joaoneves792/AviationRadio/3dmodels/potSupport.FCStd

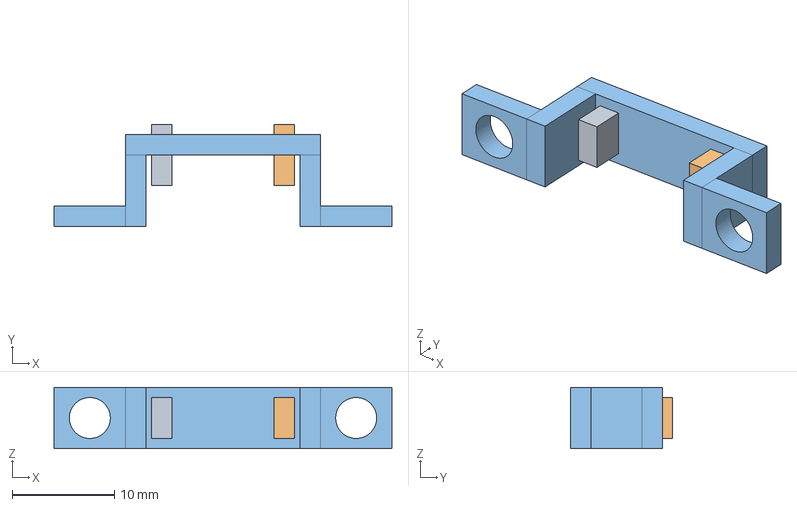
[picture p17: CAD file, 2021-02-12]
3dmodels/potSupport.FCStd
33.0 x 10.0 x 6.00 mm
