joaoneves792/AviationRadio/3dmodels/MXterst.FCStd

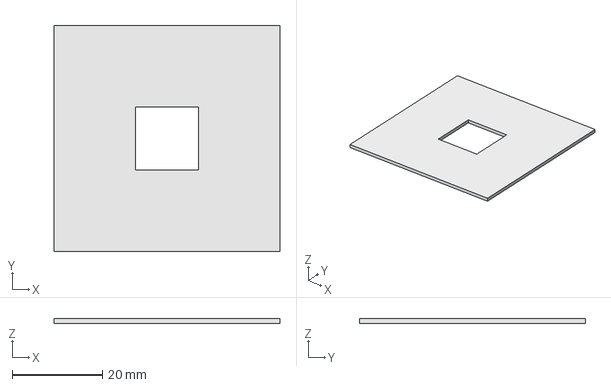
[picture p18: CAD file, 2021-02-12]
3dmodels/MXterst.FCStd
50.0 x 50.0 x 1.00 mm
