joaoneves792/AviationRadio/3dmodels/MXtest.stl

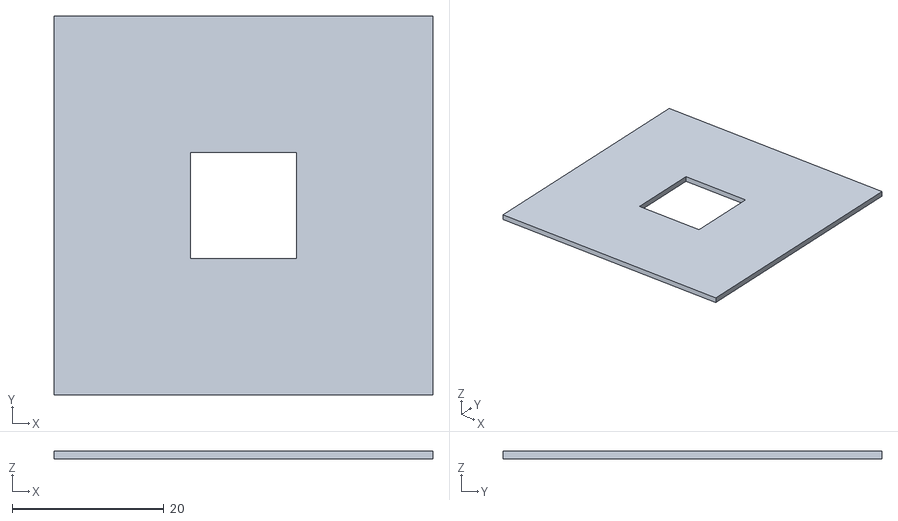
[picture p19: CAD file, 2021-02-12]
3dmodels/MXtest.stl
50.0 x 50.0 x 1.00
