joaoneves792/AviationRadio/3dmodels/FrontPanelV1.FCStd

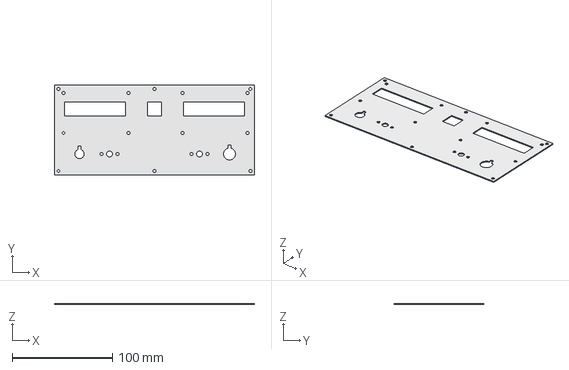
[picture p20: CAD file, 2021-02-12]
3dmodels/FrontPanelV1.FCStd
200.0 x 90.0 x 1.00 mm
