joaoneves792/AviationRadio/3dmodels/displayTest.FCStd

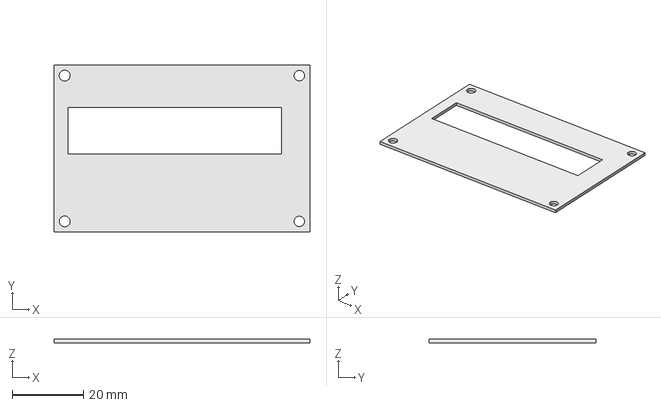
[picture p21: CAD file, 2021-02-12]
3dmodels/displayTest.FCStd
72.0 x 47.0 x 1.00 mm
